fpiesik/pMic/docs/pictures/DSC03962.JPG

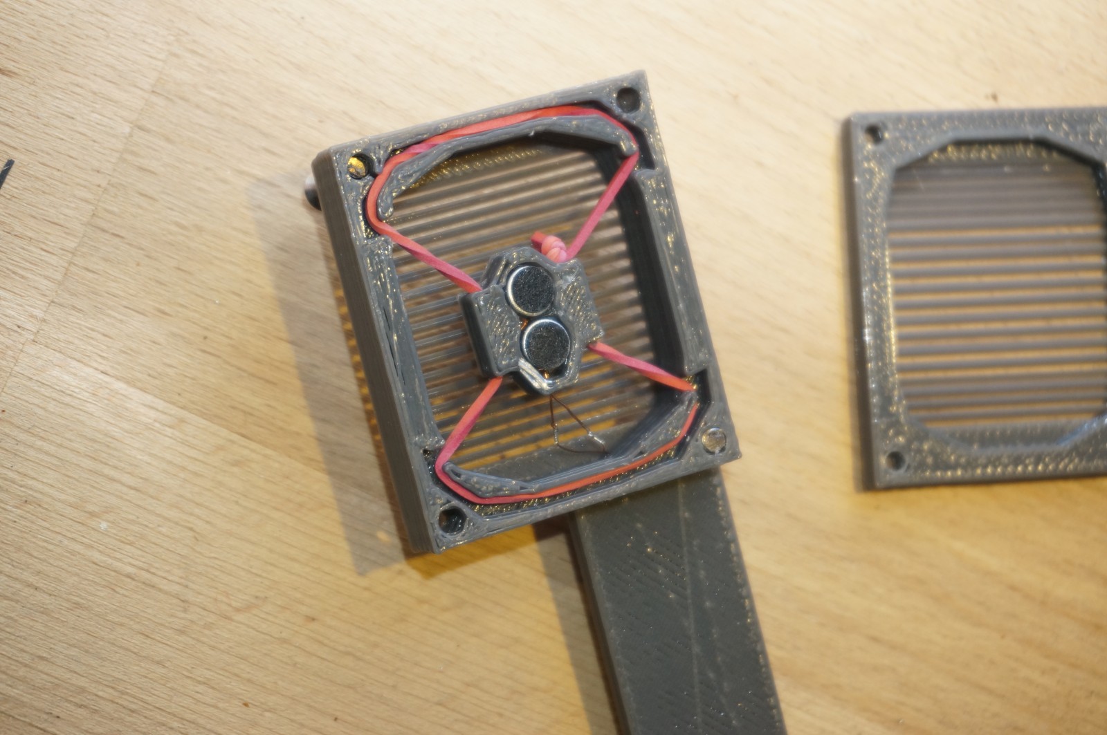
docs/pictures/DSC03962.JPG
