fpiesik/pMic/docs/pictures/DSC03967.JPG

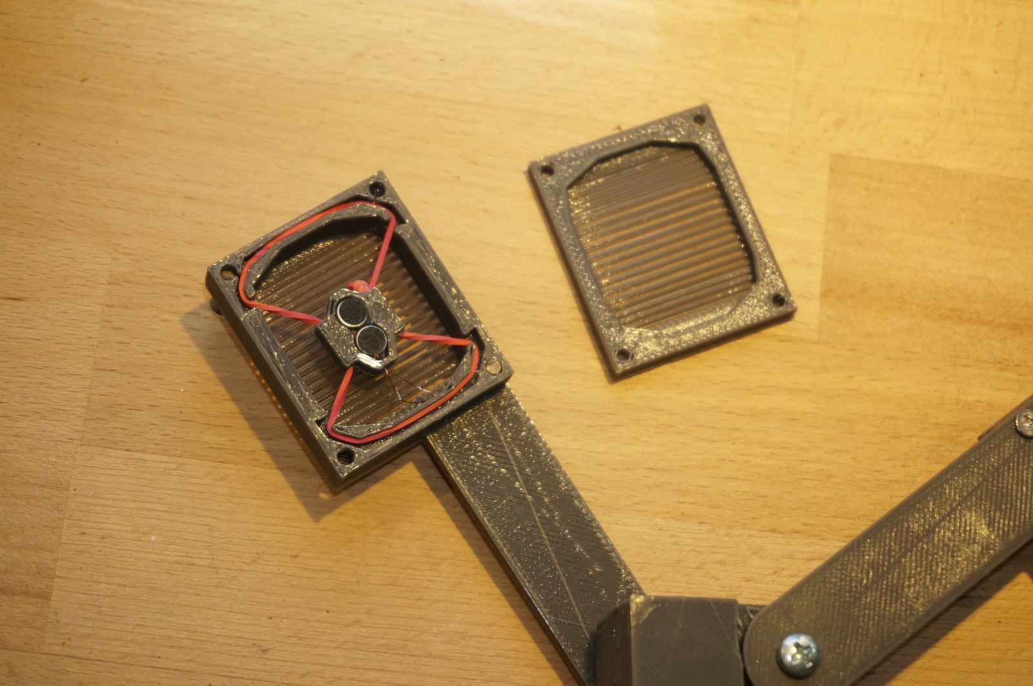
docs/pictures/DSC03967.JPG
