fpiesik/pMic/docs/pictures/DSC03972.JPG

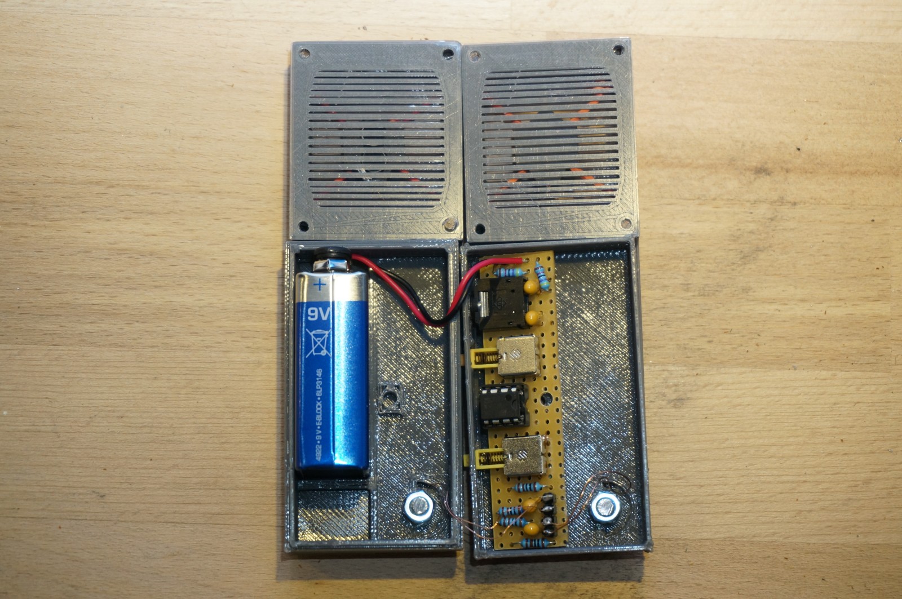
docs/pictures/DSC03972.JPG
