fpiesik/pMic/docs/pictures/DSC03975.JPG

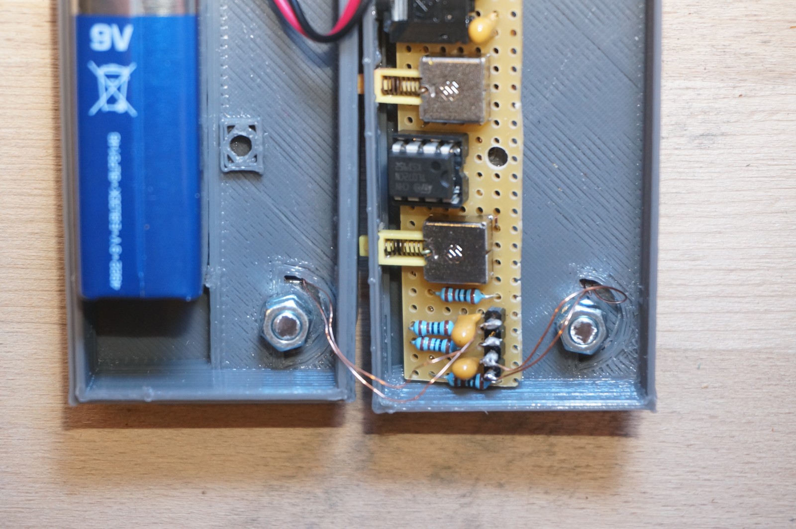
docs/pictures/DSC03975.JPG
