fpiesik/pMic/docs/pictures/DSC03977.JPG

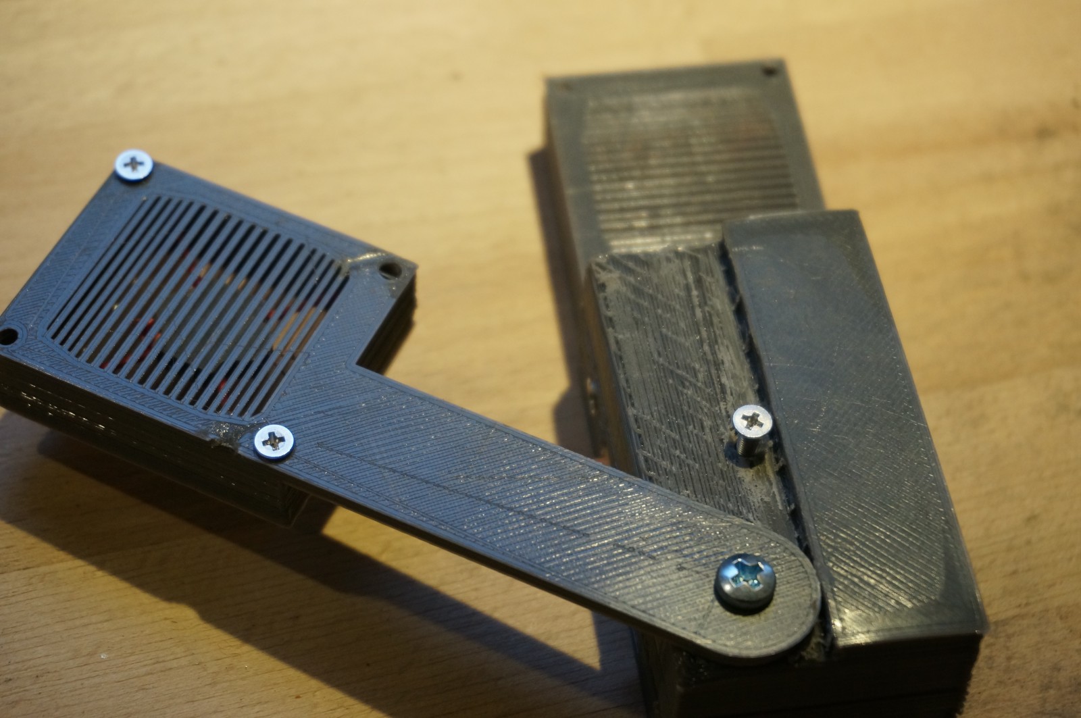
docs/pictures/DSC03977.JPG
